mjphoto/cnc_machine_mj/CAD_Files/Bike Jump/JigSaw/M_Plus_Connect_to_Medium.png

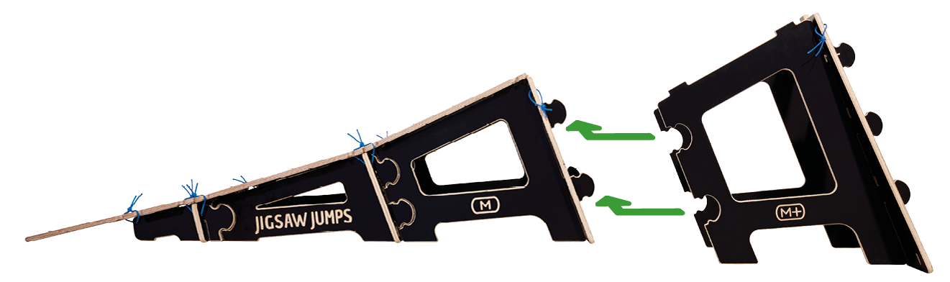
CAD_Files/Bike Jump/JigSaw/M_Plus_Connect_to_Medium.png
