mjphoto/cnc_machine_mj/CAD_Files/Bike Jump/JigSaw/M_Plus_Diagram.png

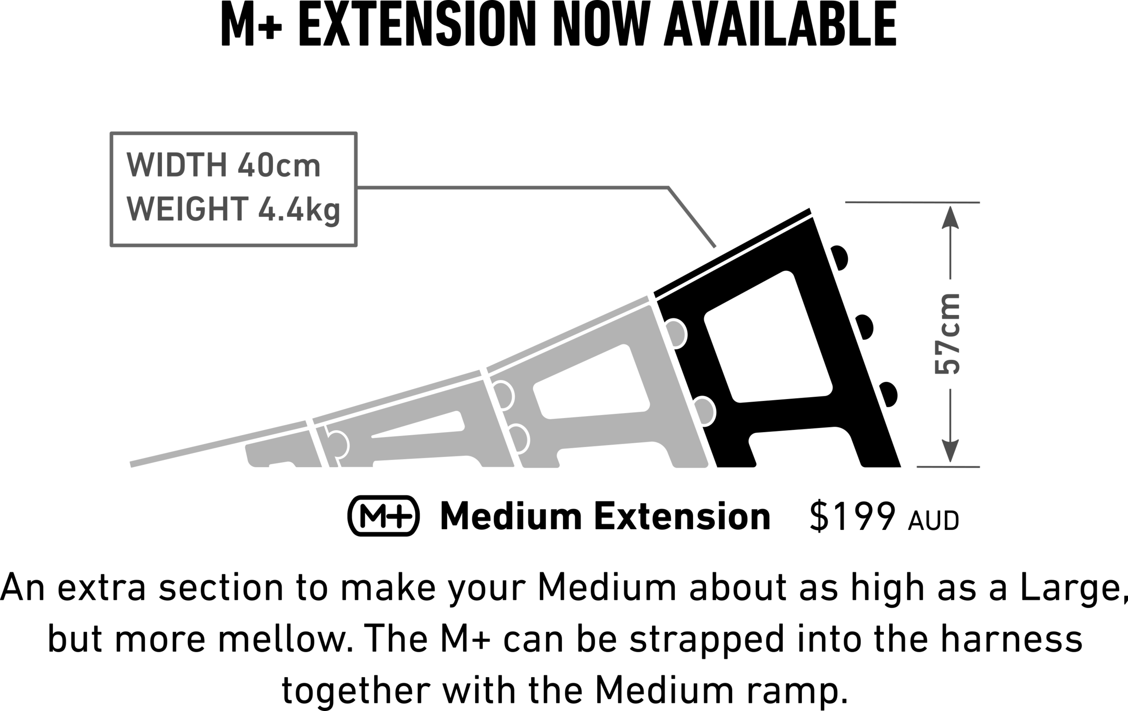
CAD_Files/Bike Jump/JigSaw/M_Plus_Diagram.png
