mjphoto/cnc_machine_mj/CAD_Files/Bike Jump/MTB Hopper/Coac and Extension.PNG

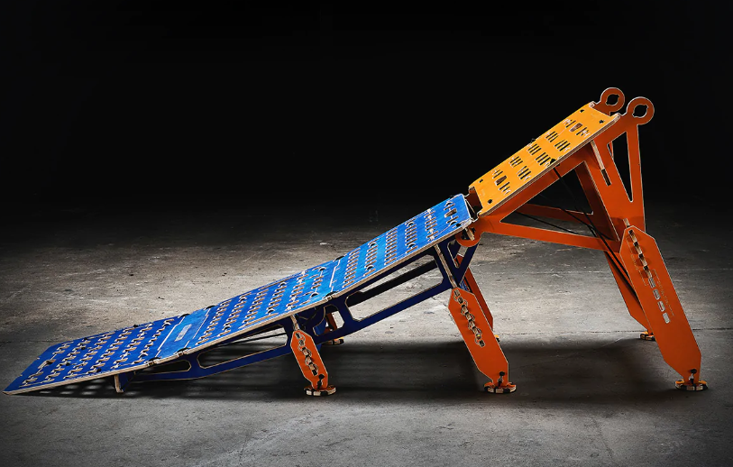
CAD_Files/Bike Jump/MTB Hopper/Coac and Extension.PNG
