mjphoto/cnc_machine_mj/CAD_Files/Bike Jump/MTB Hopper/Coach High.PNG

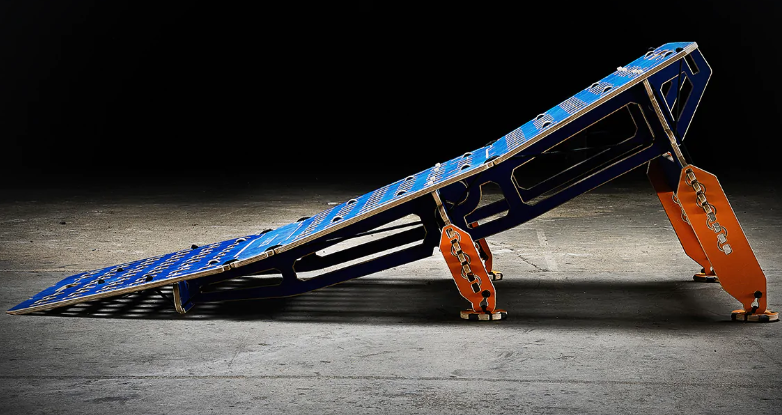
CAD_Files/Bike Jump/MTB Hopper/Coach High.PNG
