mjphoto/cnc_machine_mj/CAD_Files/Bike Jump/MTB Hopper/LITE.webp

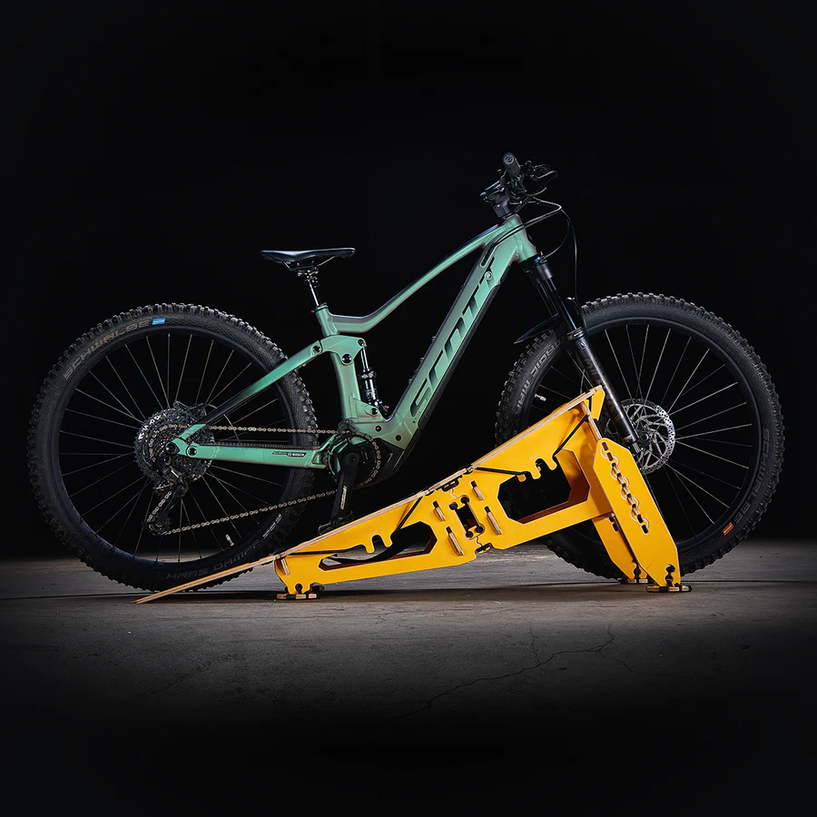
CAD_Files/Bike Jump/MTB Hopper/LITE.webp
