mjphoto/cnc_machine_mj/eyebrows/side_1655.dxf

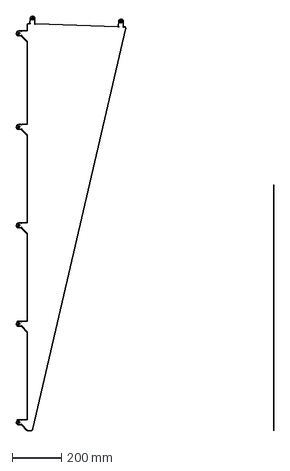
[picture p28: CAD file, 2020-05-06]
eyebrows/side_1655.dxf
1045.0 x 1684.5 mm
