mjphoto/cnc_machine_mj/CAD_CNC_Machine/CNC_Machine_CAD_Short/C-Beam End Plate.SLDPRT

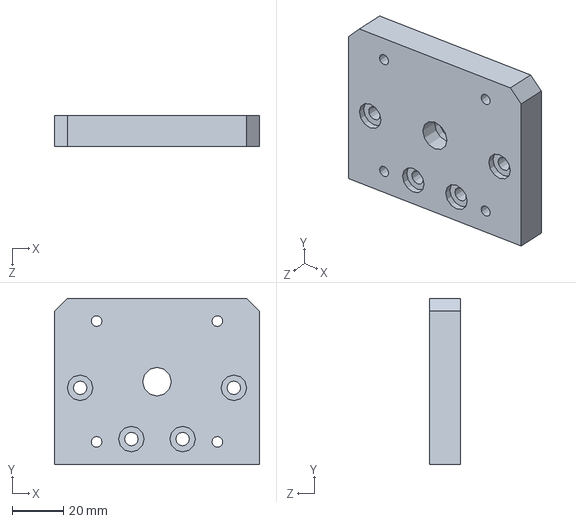
[picture p29: CAD file, 2023-01-13]
CAD_CNC_Machine/CNC_Machine_CAD_Short/C-Beam End Plate.SLDPRT
80.0 x 64.9 x 12.0 mm
