mjphoto/cnc_machine_mj/CAD_Files/Bike Jump/PBR-CON-001.SLDPRT

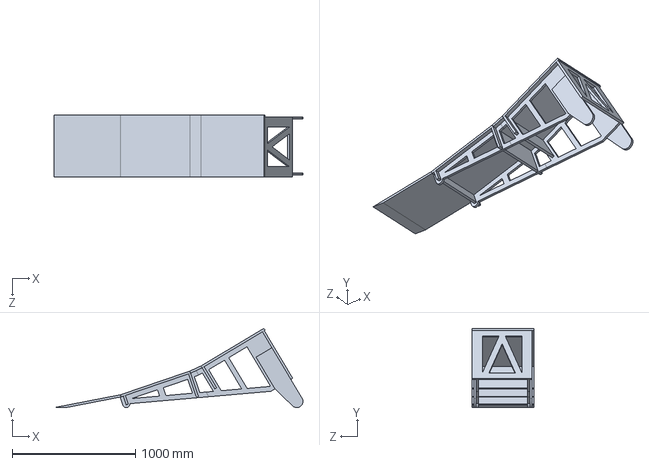
[picture p30: CAD file, 2022-08-21]
CAD_Files/Bike Jump/PBR-CON-001.SLDPRT
2021.9 x 643.9 x 500.0 mm
