mjphoto/cnc_machine_mj/CAD_Files/CNC Clamps/Clamp_130mm.STEP

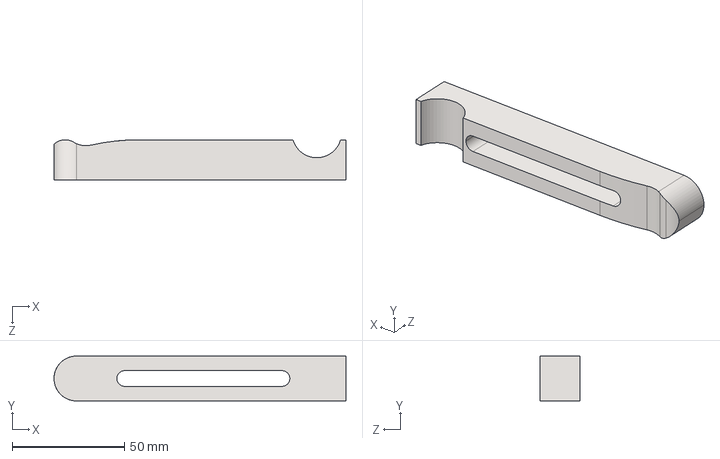
[picture p31: CAD file, 2022-08-21]
CAD_Files/CNC Clamps/Clamp_130mm.STEP
130.0 x 20.0 x 18.0 mm
