mjphoto/cnc_machine_mj/CAD_Files/Kitchen Cupboard/Wardrobe_Bench.STEP

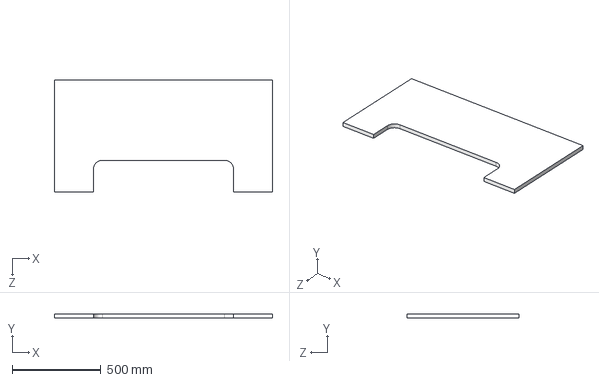
[picture p32: CAD file, 2022-09-03]
CAD_Files/Kitchen Cupboard/Wardrobe_Bench.STEP
1225.0 x 25.0 x 627.0 mm
