mjphoto/cnc_machine_mj/CAD_Files/Workbench/BenchWheelSpacer-Boss-Extrude4.STEP

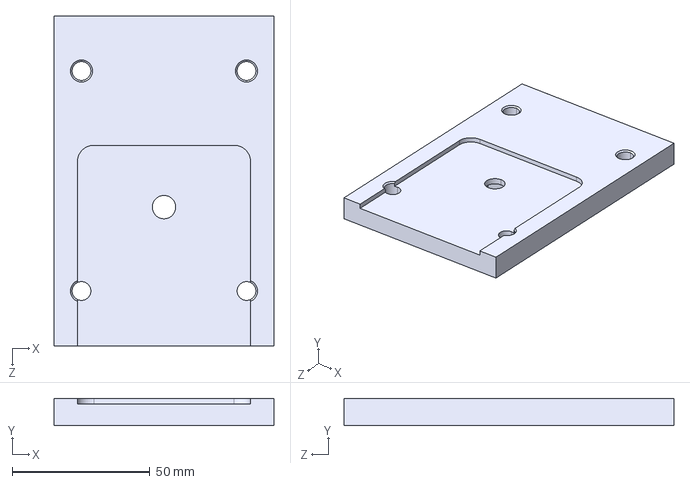
[picture p33: CAD file, 2022-08-21]
CAD_Files/Workbench/BenchWheelSpacer-Boss-Extrude4.STEP
80.0 x 10.0 x 120.0 mm
