mjphoto/cnc_machine_mj/eyebrows/side_2295.dxf

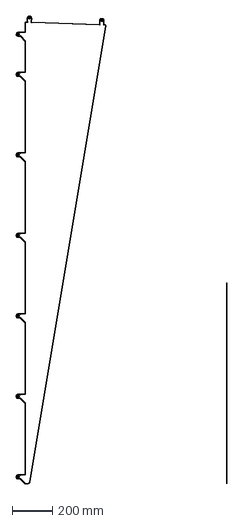
[picture p34: CAD file, 2020-05-06]
eyebrows/side_2295.dxf
1045.0 x 2324.4 mm
