mjphoto/cnc_machine_mj/CAD_Files/CNC Clamps/Clamp_110mm.STEP

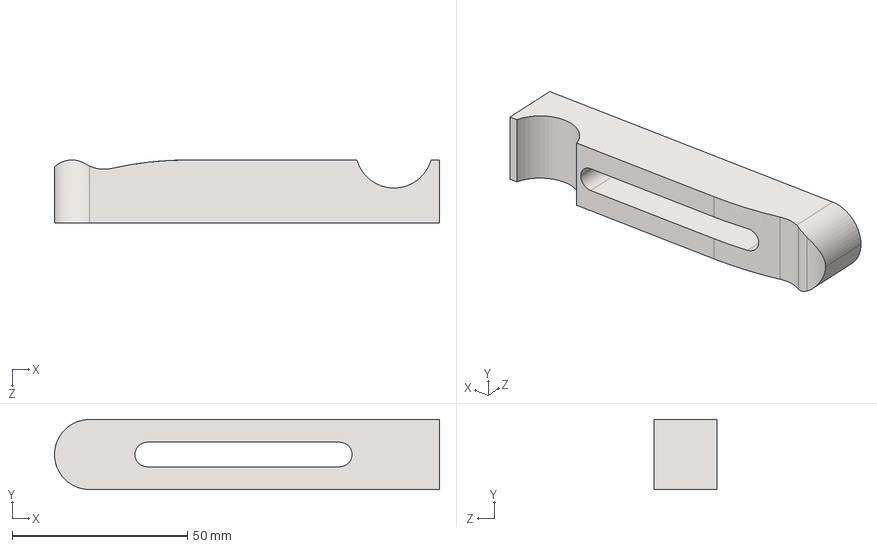
[picture p35: CAD file, 2022-08-21]
CAD_Files/CNC Clamps/Clamp_110mm.STEP
110.0 x 20.0 x 18.0 mm
