mjphoto/cnc_machine_mj/CAD_Files/Kitchen Cupboard/NEstyboi.STEP

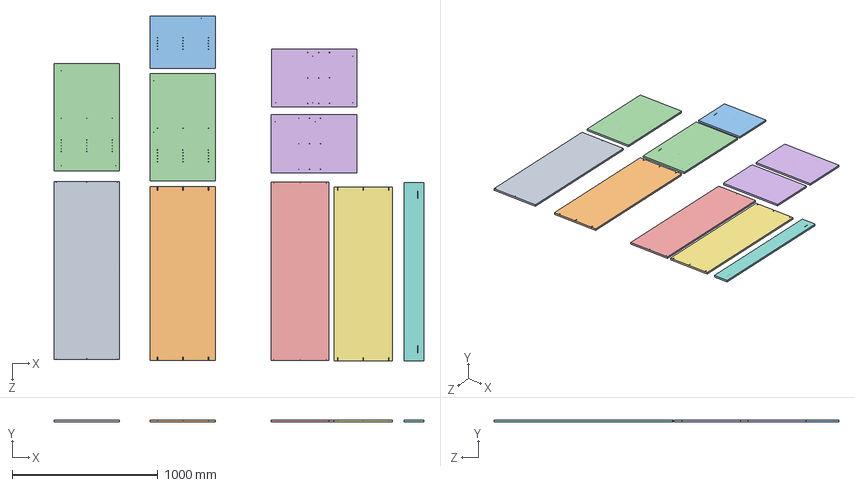
[picture p36: CAD file, 2022-09-02]
CAD_Files/Kitchen Cupboard/NEstyboi.STEP
2541.8 x 16.0 x 2369.9 mm
Wardrobe_02
Wardrobe_03
Wardrobe_04
Wardrobe_05
Wardrobe_06
Wardrobe_07
Wardrobe_08
Wardrobe_09
Wardrobe_10
Wardrobe_11
