mjphoto/cnc_machine_mj/eyebrows/side_2235.dxf

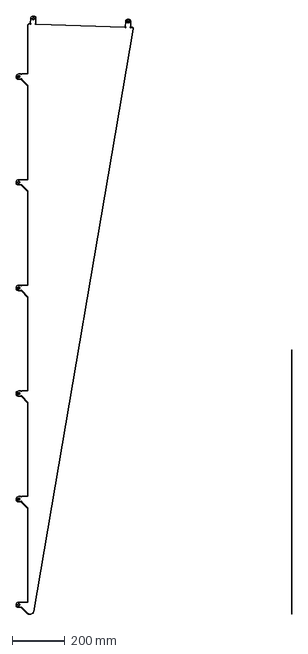
[picture p37: CAD file, 2020-05-06]
eyebrows/side_2235.dxf
1045.0 x 2264.5 mm
