mjphoto/cnc_machine_mj/CAD_Files/Baby Play Gym/PlayGym_Side_A.STEP

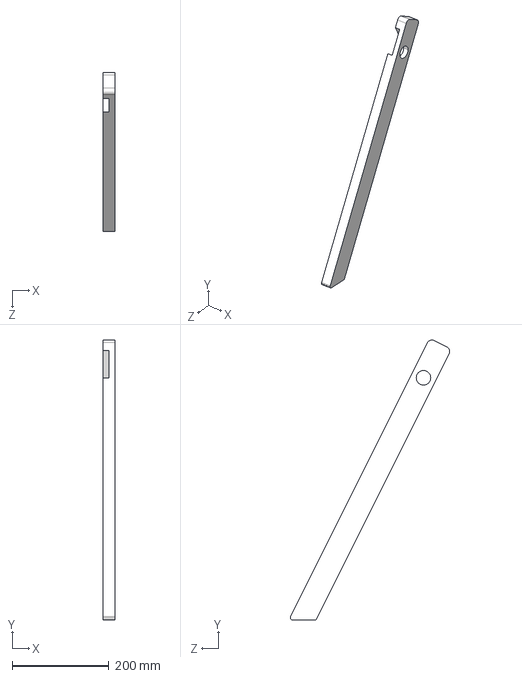
[picture p38: CAD file, 2022-09-02]
CAD_Files/Baby Play Gym/PlayGym_Side_A.STEP
25.0 x 578.0 x 328.9 mm
