mjphoto/cnc_machine_mj/eyebrows/side_1855.dxf

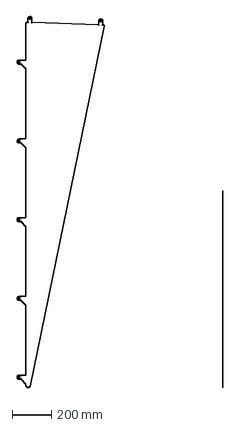
[picture p39: CAD file, 2020-05-06]
eyebrows/side_1855.dxf
1045.0 x 1884.5 mm
