mjphoto/cnc_machine_mj/CAD_CNC_Machine/CNC_Machine_CAD_Short/CNC_SHORT_MGN12H1R100ZFC.SLDPRT

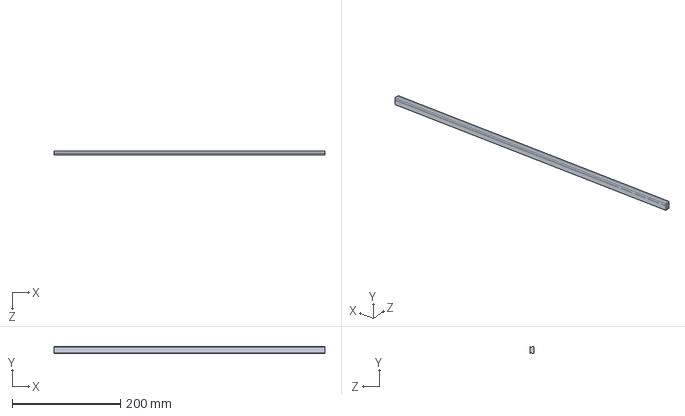
[picture p40: CAD file, 2023-01-13]
CAD_CNC_Machine/CNC_Machine_CAD_Short/CNC_SHORT_MGN12H1R100ZFC.SLDPRT
500.0 x 12.0 x 8.00 mm
