mjphoto/cnc_machine_mj/eyebrows/Verandah_plates.dxf

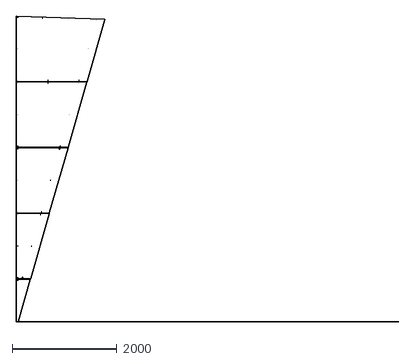
[picture p41: CAD file, 2020-05-05]
eyebrows/Verandah_plates.dxf
7301.5 x 5836.0
