mjphoto/cnc_machine_mj/CAD_CNC_Machine/CNC_Machine_CAD_Short/V-Slot C-Beam.SLDPRT

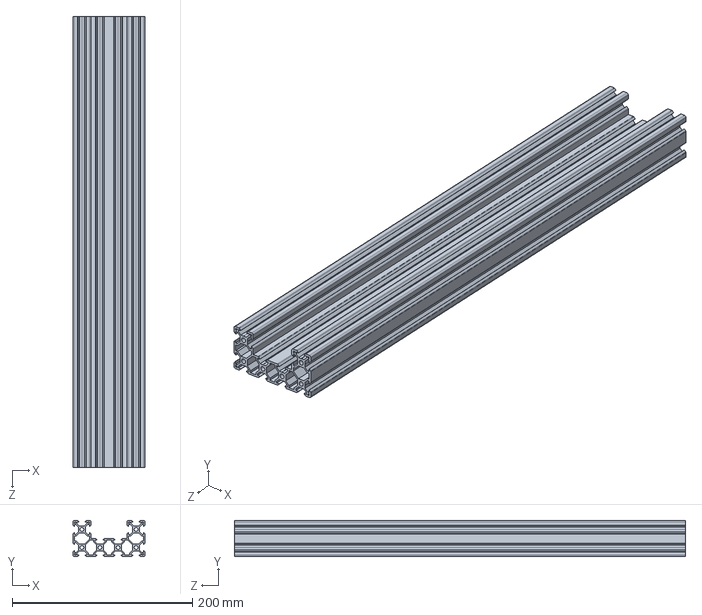
[picture p42: CAD file, 2023-01-13]
CAD_CNC_Machine/CNC_Machine_CAD_Short/V-Slot C-Beam.SLDPRT
80.0 x 40.0 x 500.0 mm
