mjphoto/cnc_machine_mj/CAD_CNC_Machine/CNC_Machine_CAD_Short/CNC_SHORT_X Axis Tall Front Plate_6mm - Build 80_11.15.14.SLDPRT

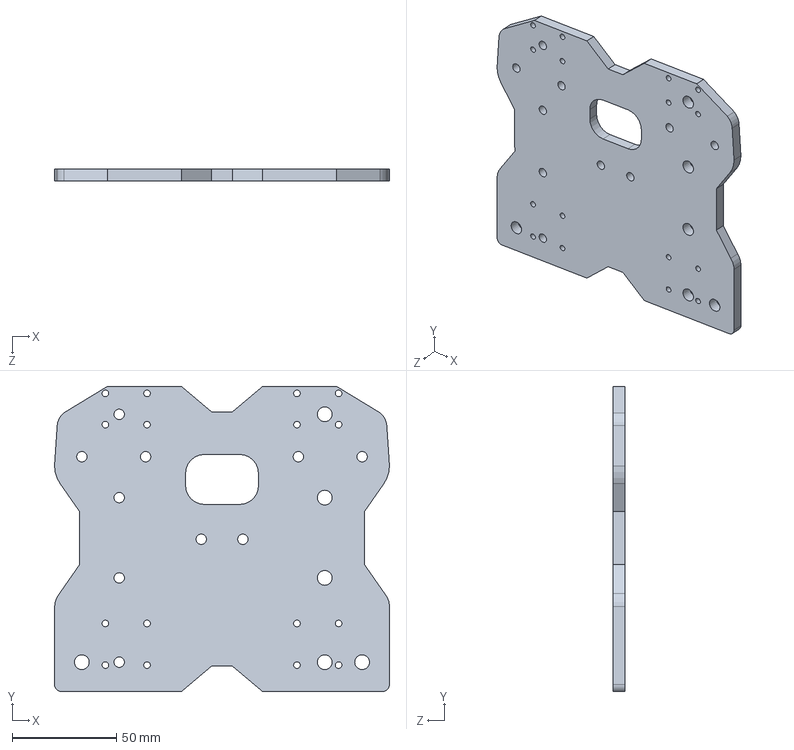
[picture p43: CAD file, 2023-01-13]
CAD_CNC_Machine/CNC_Machine_CAD_Short/CNC_SHORT_X Axis Tall Front Plate_6mm - Build 80_11.15.14.SLDPRT
160.9 x 146.5 x 6.00 mm
