mjphoto/cnc_machine_mj/CAD_CNC_Machine/CNC_Machine_CAD_Short/CNC_SHORT_V-Slot 20x80x1500 Linear Rail.SLDPRT

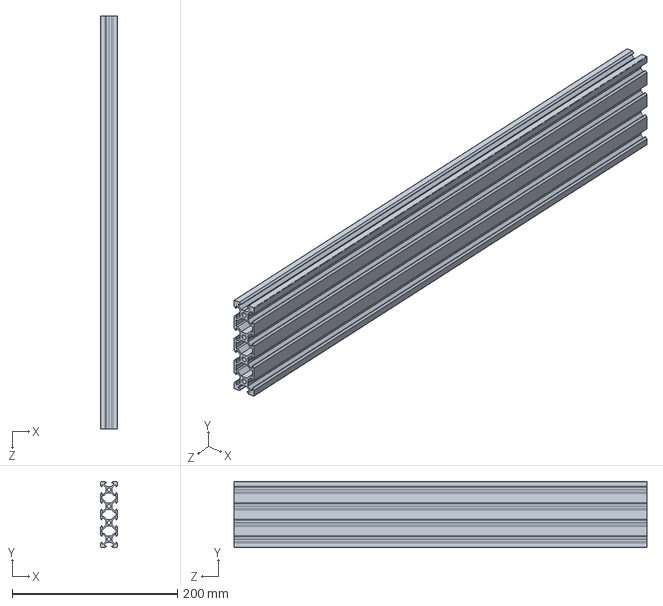
[picture p44: CAD file, 2022-12-09]
CAD_CNC_Machine/CNC_Machine_CAD_Short/CNC_SHORT_V-Slot 20x80x1500 Linear Rail.SLDPRT
20.0 x 80.0 x 500.0 mm
