mjphoto/cnc_machine_mj/CAD_CNC_Machine/CNC_Machine_CAD_Short/CNC_SHORT_Frame2.SLDPRT

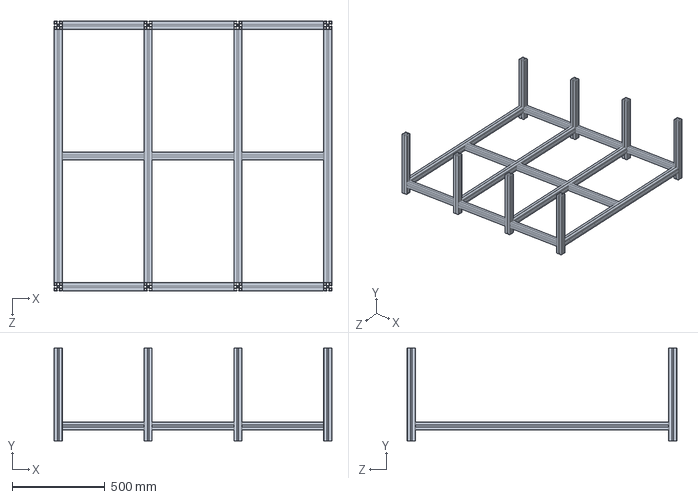
[picture p45: CAD file, 2022-12-09]
CAD_CNC_Machine/CNC_Machine_CAD_Short/CNC_SHORT_Frame2.SLDPRT
1500.0 x 500.0 x 1455.0 mm
