mjphoto/cnc_machine_mj/CAD_CNC_Machine/CNC_Machine_CAD_Short/CNC_SHORT_Table minitec.SLDPRT

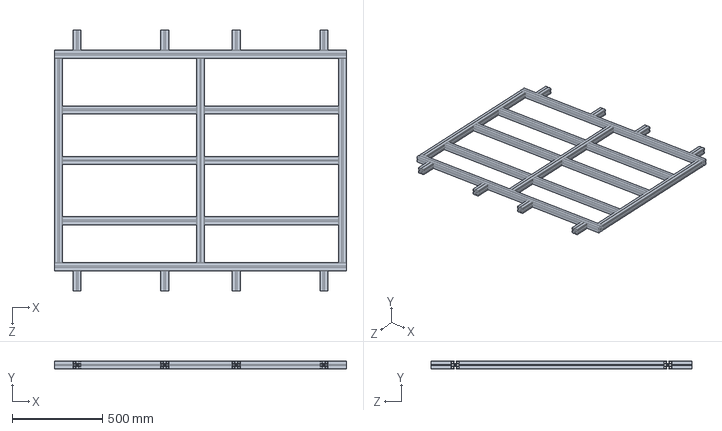
[picture p46: CAD file, 2022-12-09]
CAD_CNC_Machine/CNC_Machine_CAD_Short/CNC_SHORT_Table minitec.SLDPRT
1615.0 x 45.0 x 1445.0 mm
