mjphoto/cnc_machine_mj/CAD_CNC_Machine/CNC_Machine_CAD_Short/CNC_SHORT_V-Slot 20x40x1500 Linear Rail.SLDPRT

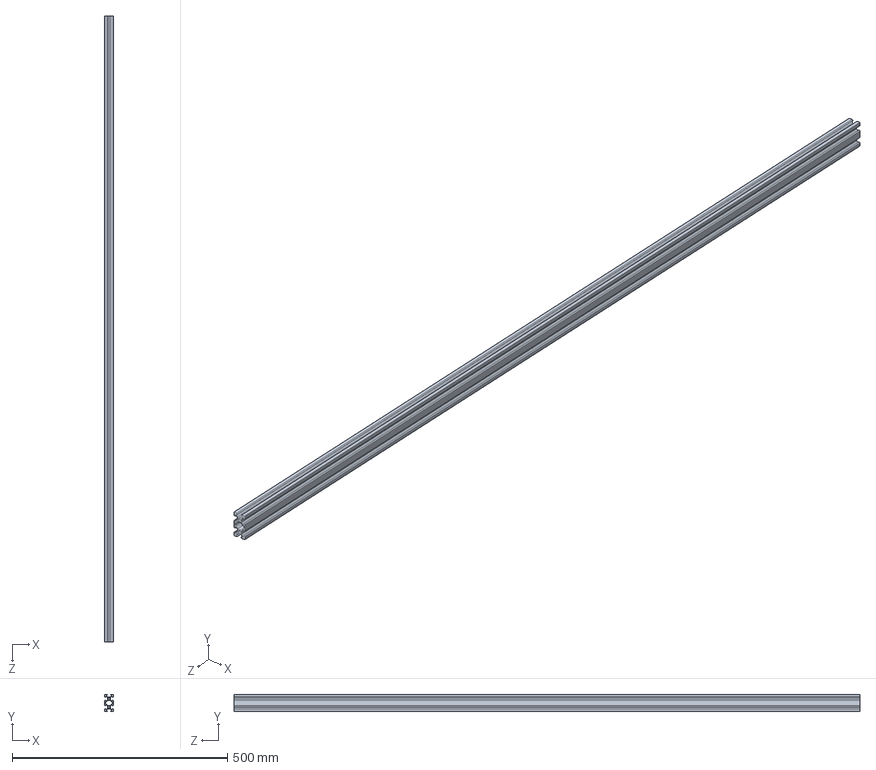
[picture p47: CAD file, 2022-12-09]
CAD_CNC_Machine/CNC_Machine_CAD_Short/CNC_SHORT_V-Slot 20x40x1500 Linear Rail.SLDPRT
20.0 x 40.0 x 1455.0 mm
