mjphoto/cnc_machine_mj/CAD_CNC_Machine/CNC_Machine_CAD_Short/CNC_SHORT_Eccentric Spacer 6mm.SLDPRT

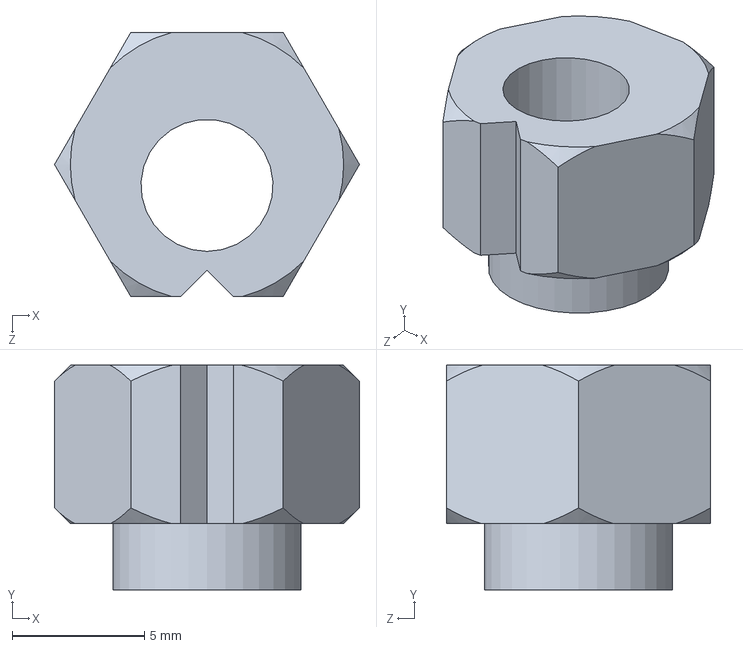
[picture p48: CAD file, 2022-11-07]
CAD_CNC_Machine/CNC_Machine_CAD_Short/CNC_SHORT_Eccentric Spacer 6mm.SLDPRT
11.5 x 8.50 x 10.0 mm
