mjphoto/cnc_machine_mj/CAD_CNC_Machine/CNC_Machine_CAD_Short/CNC_SHORT_GT3 Timing Pulley 20 Tooth.SLDPRT

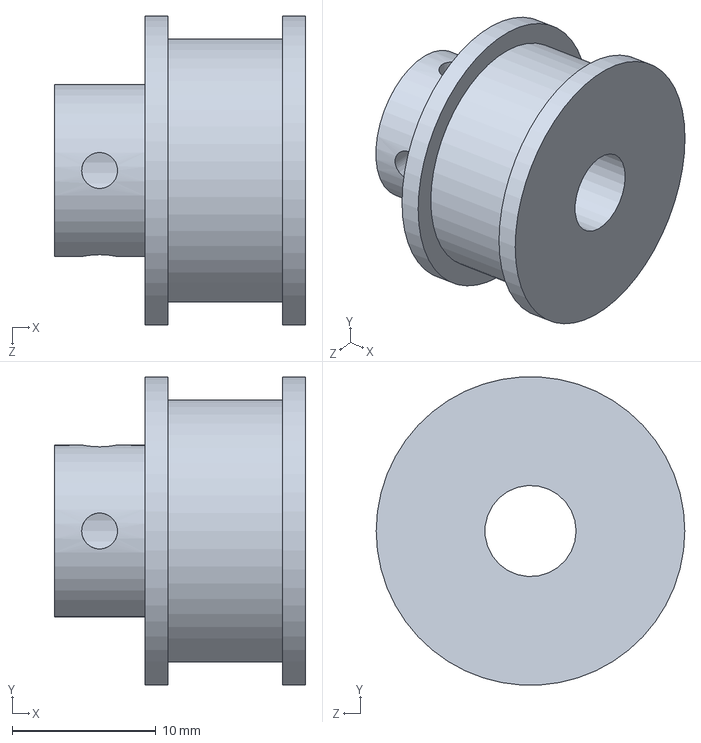
[picture p49: CAD file, 2022-11-07]
CAD_CNC_Machine/CNC_Machine_CAD_Short/CNC_SHORT_GT3 Timing Pulley 20 Tooth.SLDPRT
17.5 x 21.5 x 21.5 mm
