mjphoto/cnc_machine_mj/CAD_CNC_Machine/CNC_Machine_CAD_Short/CNC_SHORT_Aluminum Spacer 9mm.SLDPRT

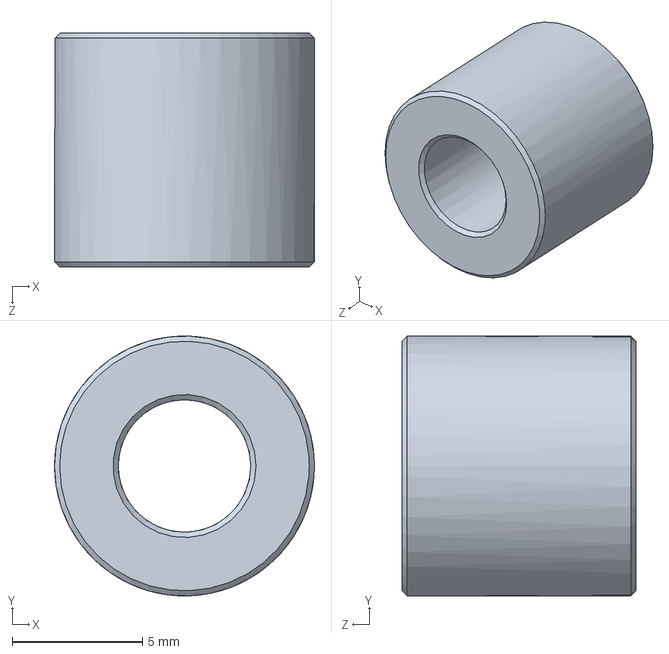
[picture p50: CAD file, 2022-11-07]
CAD_CNC_Machine/CNC_Machine_CAD_Short/CNC_SHORT_Aluminum Spacer 9mm.SLDPRT
10.0 x 9.99 x 9.00 mm
