mjphoto/cnc_machine_mj/CAD_CNC_Machine/CNC_Machine_CAD_Short/CNC_SHORT_Spindle.SLDPRT

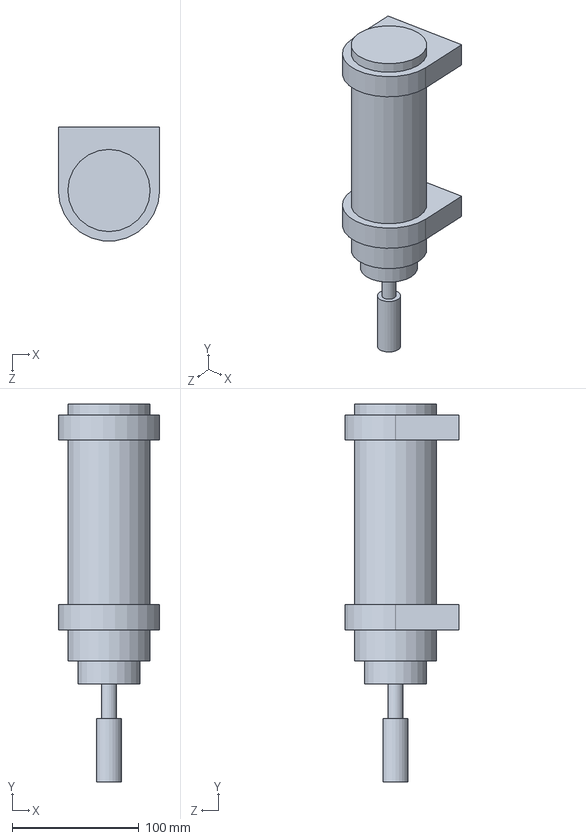
[picture p51: CAD file, 2022-11-07]
CAD_CNC_Machine/CNC_Machine_CAD_Short/CNC_SHORT_Spindle.SLDPRT
80.0 x 298.5 x 89.7 mm
