mjphoto/cnc_machine_mj/CAD_CNC_Machine/CNC_Machine_CAD_Short/CNC_SHORT_Spoil.SLDPRT

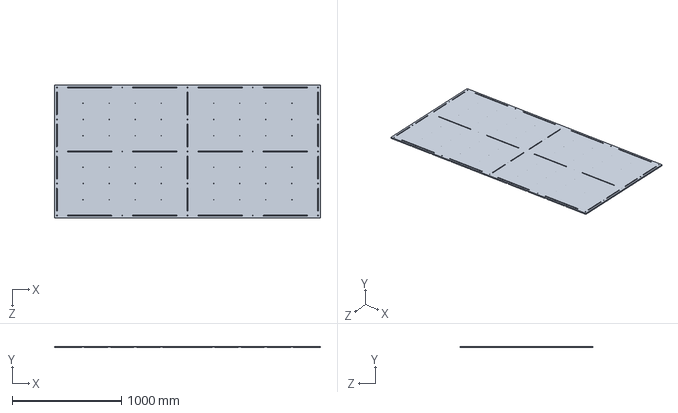
[picture p52: CAD file, 2022-11-07]
CAD_CNC_Machine/CNC_Machine_CAD_Short/CNC_SHORT_Spoil.SLDPRT
2440.0 x 12.0 x 1220.0 mm
