mjphoto/cnc_machine_mj/CAD_CNC_Machine/CNC_Machine_CAD_Short/CNC_SHORT_Precision Shim 10 x 5 x 1.SLDPRT

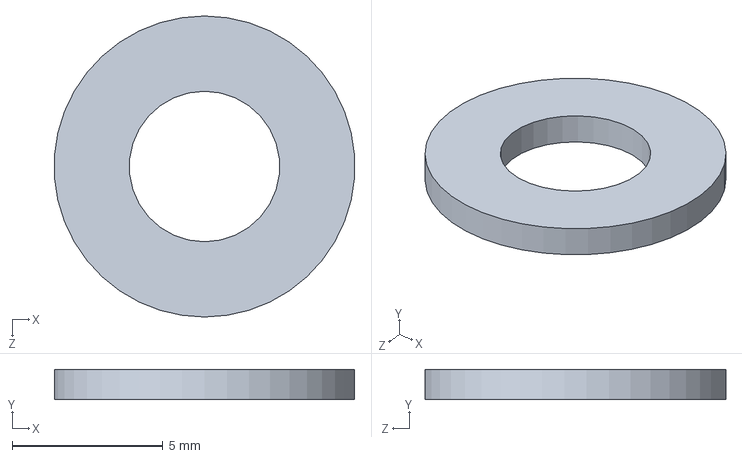
[picture p53: CAD file, 2022-11-07]
CAD_CNC_Machine/CNC_Machine_CAD_Short/CNC_SHORT_Precision Shim 10 x 5 x 1.SLDPRT
9.97 x 1.00 x 10.0 mm
