mjphoto/cnc_machine_mj/CAD_CNC_Machine/CNC_Machine_CAD_Short/CNC_SHORT_Y Gantry Plate_6mm - Build 80_11.15.14.SLDPRT

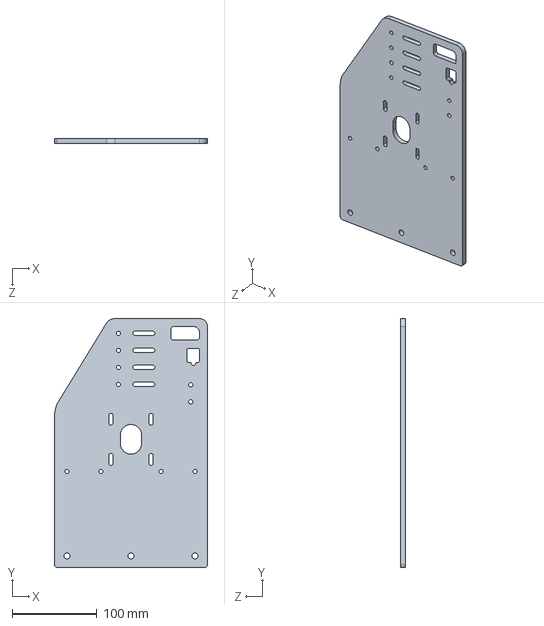
[picture p54: CAD file, 2022-11-07]
CAD_CNC_Machine/CNC_Machine_CAD_Short/CNC_SHORT_Y Gantry Plate_6mm - Build 80_11.15.14.SLDPRT
180.0 x 293.0 x 6.00 mm
