mjphoto/cnc_machine_mj/CAD_CNC_Machine/CNC_Machine_CAD_Short/CNC_SHORT_Spindle Holder.SLDPRT

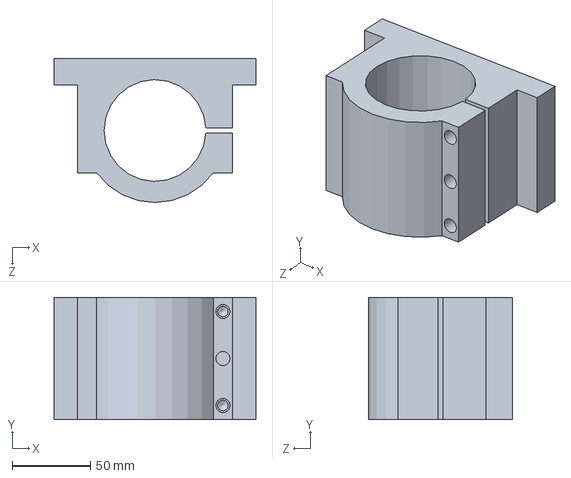
[picture p55: CAD file, 2022-11-07]
CAD_CNC_Machine/CNC_Machine_CAD_Short/CNC_SHORT_Spindle Holder.SLDPRT
129.0 x 78.0 x 92.0 mm
