mjphoto/cnc_machine_mj/CAD_CNC_Machine/CNC_Machine_CAD_Short/CNC_SHORT_Tensioning Bracket.SLDPRT

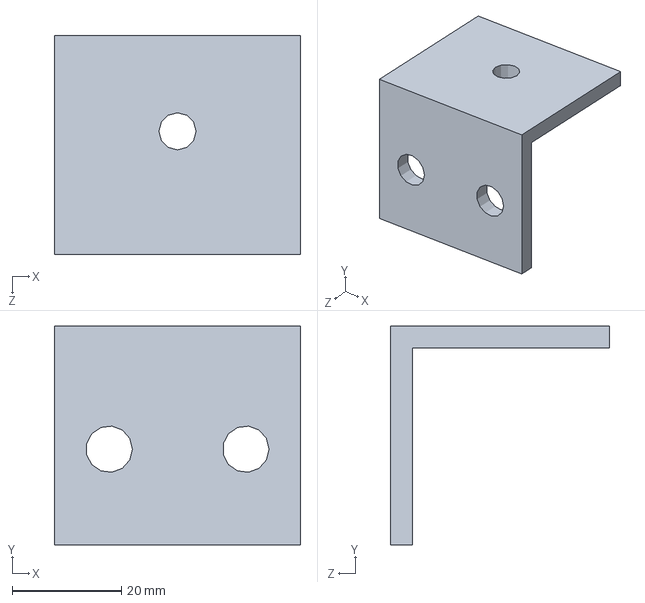
[picture p56: CAD file, 2022-11-07]
CAD_CNC_Machine/CNC_Machine_CAD_Short/CNC_SHORT_Tensioning Bracket.SLDPRT
45.0 x 40.0 x 40.0 mm
