mjphoto/cnc_machine_mj/CAD_CNC_Machine/CNC_Machine_CAD_Short/CNC_SHORT_2020.SLDPRT

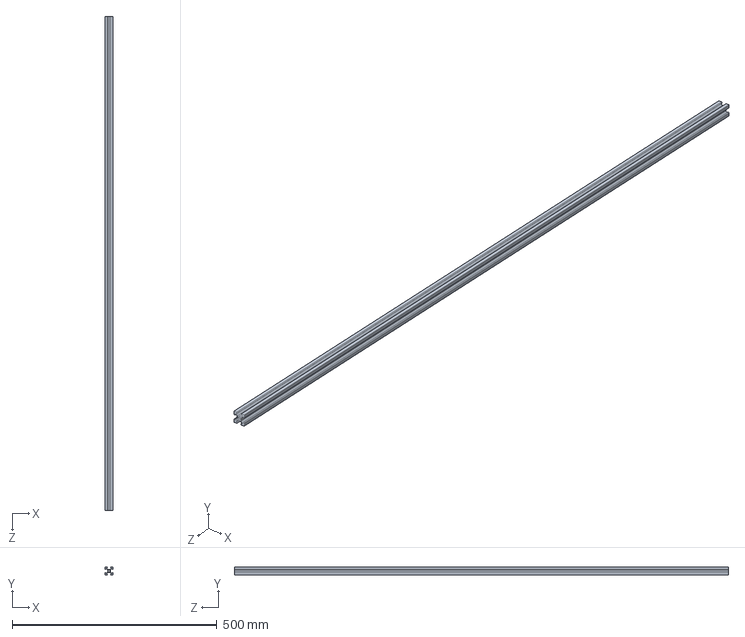
[picture p57: CAD file, 2022-11-07]
CAD_CNC_Machine/CNC_Machine_CAD_Short/CNC_SHORT_2020.SLDPRT
20.0 x 20.0 x 1205.0 mm
