mjphoto/cnc_machine_mj/CAD_CNC_Machine/CNC_Machine_CAD_Short/CNC_SHORT_Nema 23 Stepper Motor.SLDPRT

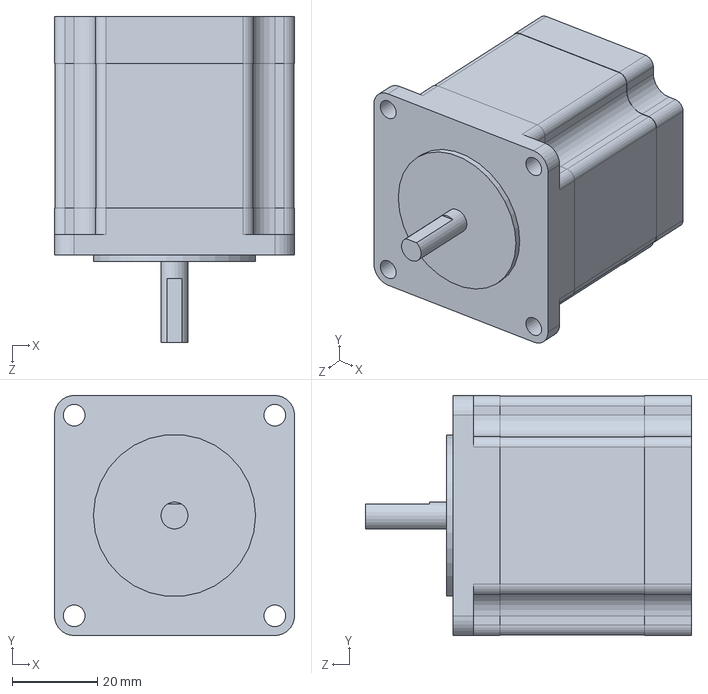
[picture p58: CAD file, 2022-11-07]
CAD_CNC_Machine/CNC_Machine_CAD_Short/CNC_SHORT_Nema 23 Stepper Motor.SLDPRT
56.4 x 56.4 x 76.6 mm
