mjphoto/cnc_machine_mj/CAD_CNC_Machine/CNC_Machine_CAD_Short/CNC_SHORT_Aluminium bed threaded bar.SLDPRT

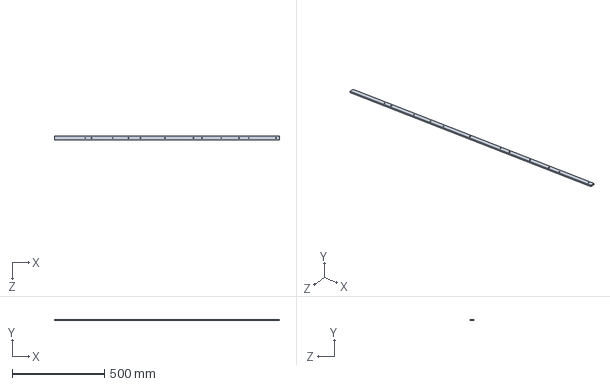
[picture p59: CAD file, 2022-11-07]
CAD_CNC_Machine/CNC_Machine_CAD_Short/CNC_SHORT_Aluminium bed threaded bar.SLDPRT
1220.0 x 6.00 x 20.0 mm
