mjphoto/cnc_machine_mj/CAD_CNC_Machine/CNC_Machine_CAD_Short/CNC_SHORT_L Bracket Single.SLDPRT

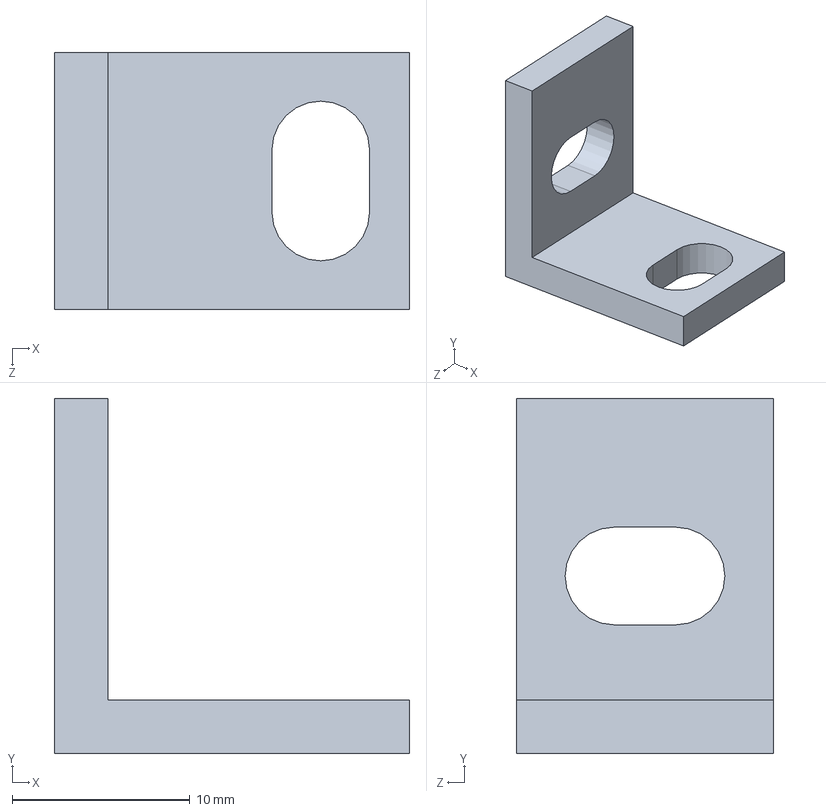
[picture p60: CAD file, 2022-11-07]
CAD_CNC_Machine/CNC_Machine_CAD_Short/CNC_SHORT_L Bracket Single.SLDPRT
20.0 x 20.0 x 14.5 mm
