mjphoto/cnc_machine_mj/CAD_CNC_Machine/CNC_Machine_CAD_Short/CNC_SHORT_MGN15H1R100ZFC.SLDPRT

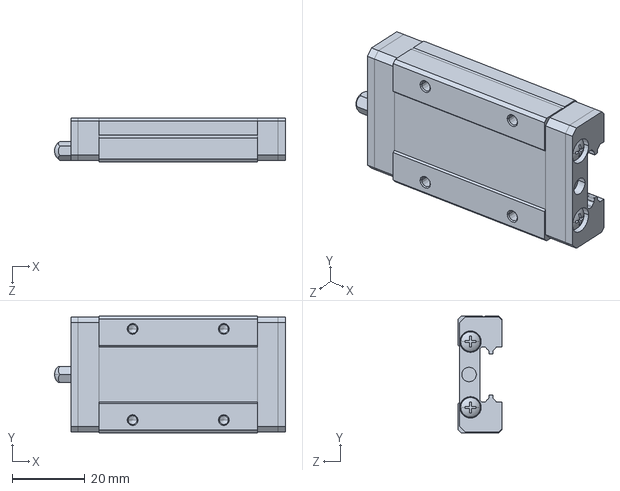
[picture p61: CAD file, 2022-11-07]
CAD_CNC_Machine/CNC_Machine_CAD_Short/CNC_SHORT_MGN15H1R100ZFC.SLDPRT
63.3 x 32.0 x 12.0 mm
