mjphoto/cnc_machine_mj/CAD_CNC_Machine/CNC_Machine_CAD_Short/CNC_SHORT_Aluminum Spacer 40mm.SLDPRT

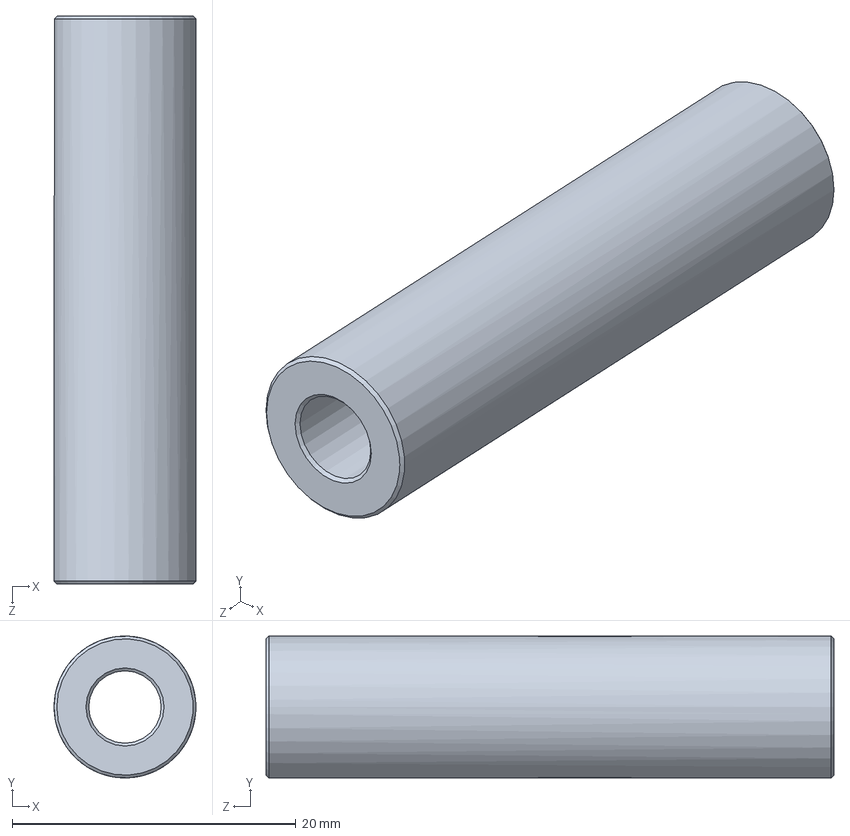
[picture p62: CAD file, 2022-11-07]
CAD_CNC_Machine/CNC_Machine_CAD_Short/CNC_SHORT_Aluminum Spacer 40mm.SLDPRT
10.0 x 9.99 x 40.0 mm
