mjphoto/cnc_machine_mj/CAD_CNC_Machine/CNC_Machine_CAD_Short/CNC_SHORT_BedBoardV2.SLDPRT

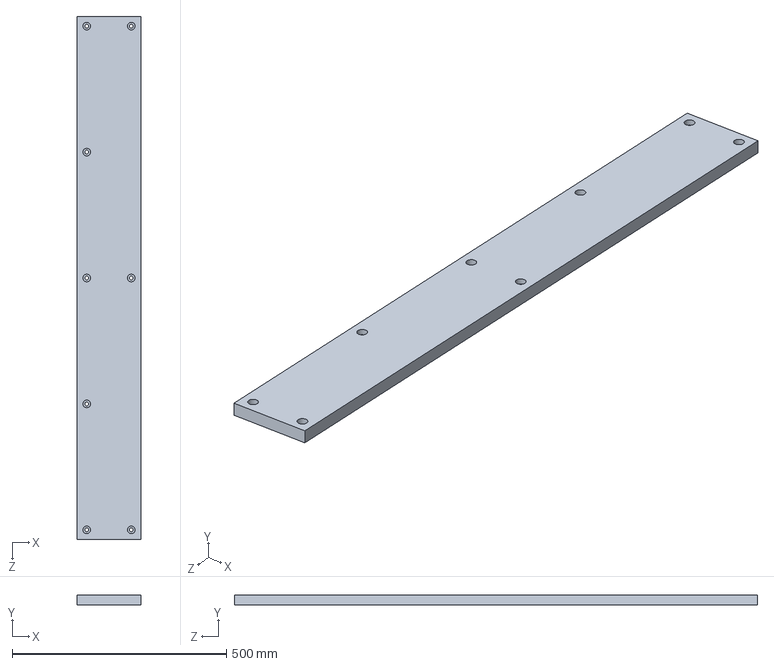
[picture p63: CAD file, 2022-11-07]
CAD_CNC_Machine/CNC_Machine_CAD_Short/CNC_SHORT_BedBoardV2.SLDPRT
148.9 x 23.0 x 1220.0 mm
