mjphoto/cnc_machine_mj/CAD_CNC_Machine/CNC_Machine_CAD_Short/CNC_SHORT_CNC-01-1015.SLDPRT

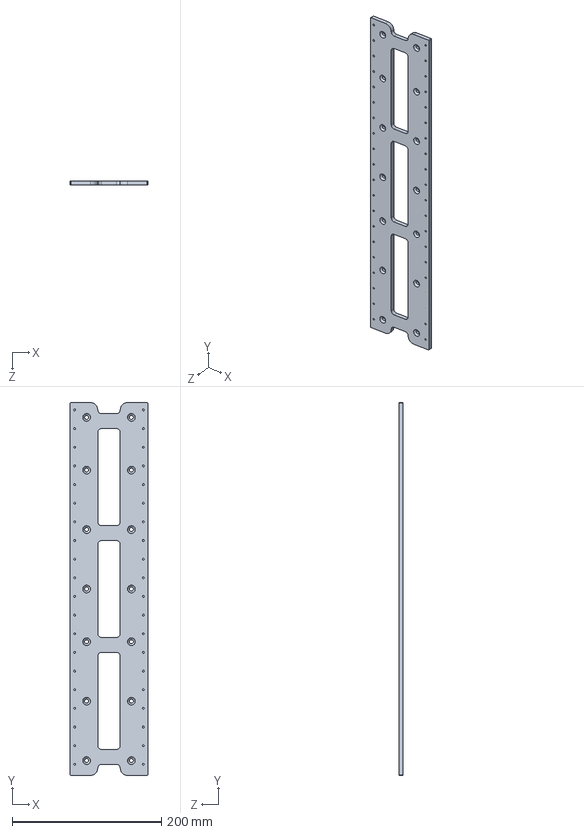
[picture p64: CAD file, 2022-11-07]
CAD_CNC_Machine/CNC_Machine_CAD_Short/CNC_SHORT_CNC-01-1015.SLDPRT
104.0 x 500.0 x 6.00 mm
