mjphoto/cnc_machine_mj/CAD_CNC_Machine/CNC_Machine_CAD_Short/CNC_SHORT_Lock Collar 8mm.SLDPRT

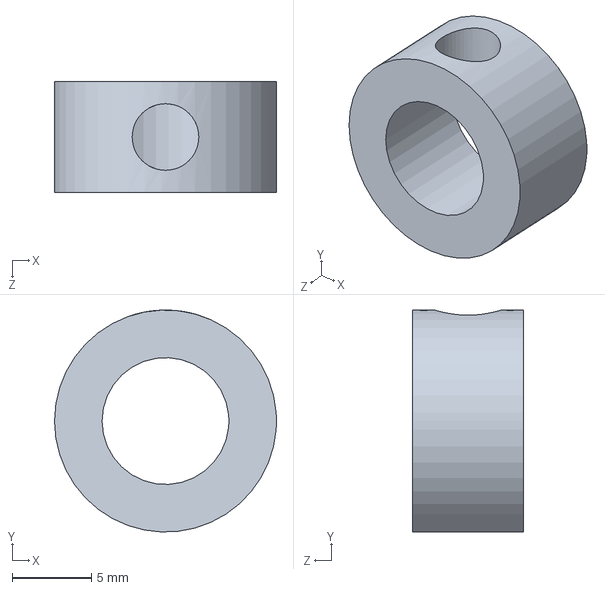
[picture p65: CAD file, 2022-11-07]
CAD_CNC_Machine/CNC_Machine_CAD_Short/CNC_SHORT_Lock Collar 8mm.SLDPRT
14.0 x 14.0 x 7.00 mm
