mjphoto/cnc_machine_mj/CAD_CNC_Machine/CNC_Machine_CAD_Short/CNC_SHORT_MGN12C1R100ZFC.SLDPRT

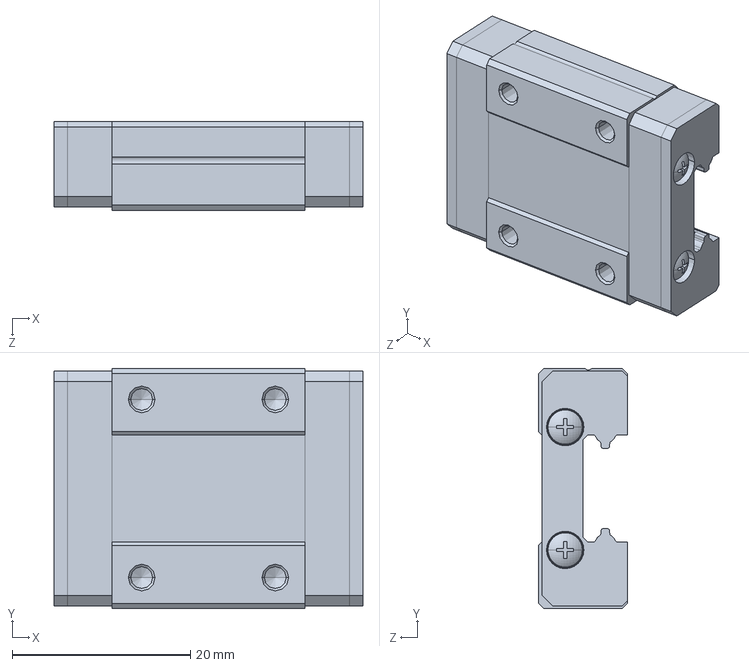
[picture p66: CAD file, 2022-11-07]
CAD_CNC_Machine/CNC_Machine_CAD_Short/CNC_SHORT_MGN12C1R100ZFC.SLDPRT
34.7 x 27.0 x 10.0 mm
