mjphoto/cnc_machine_mj/CAD_CNC_Machine/CNC_Machine_CAD_Short/CNC_SHORT_Micro Limit Switch.SLDPRT

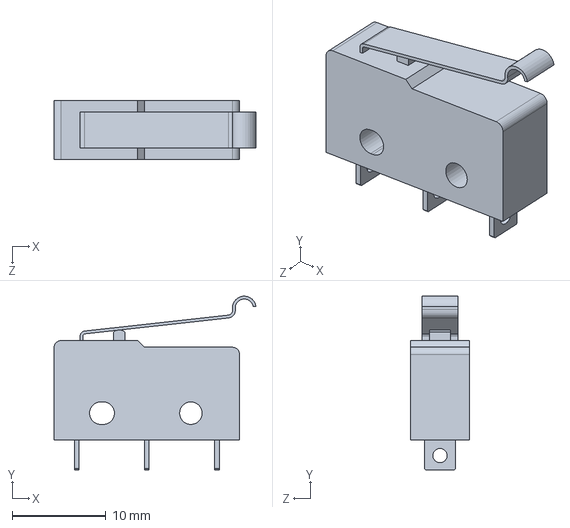
[picture p67: CAD file, 2022-11-07]
CAD_CNC_Machine/CNC_Machine_CAD_Short/CNC_SHORT_Micro Limit Switch.SLDPRT
21.6 x 18.6 x 6.35 mm
