mjphoto/cnc_machine_mj/CAD_CNC_Machine/CNC_Machine_CAD_Short/CNC_SHORT_COLLET ER11 d6-.SLDPRT

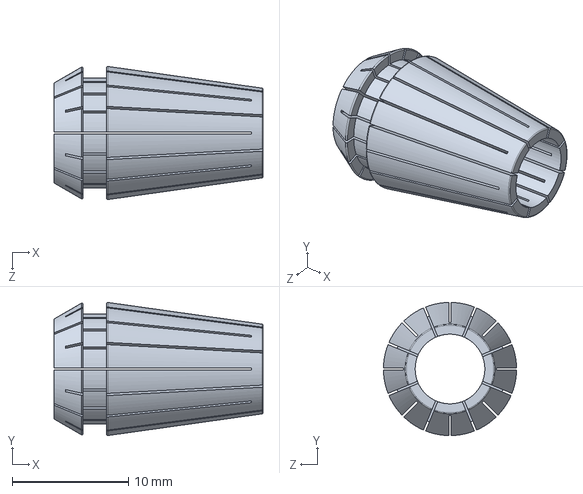
[picture p68: CAD file, 2022-11-07]
CAD_CNC_Machine/CNC_Machine_CAD_Short/CNC_SHORT_COLLET ER11 d6-.SLDPRT
18.0 x 11.5 x 11.5 mm
