mjphoto/cnc_machine_mj/CAD_CNC_Machine/CNC_Machine_CAD_Short/CNC_SHORT_Angle Bracket - 2080-4545.SLDPRT

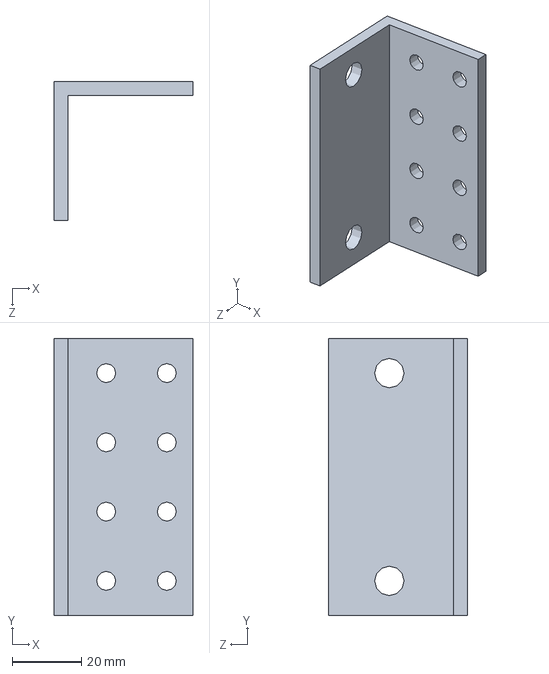
[picture p69: CAD file, 2022-11-07]
CAD_CNC_Machine/CNC_Machine_CAD_Short/CNC_SHORT_Angle Bracket - 2080-4545.SLDPRT
40.0 x 80.0 x 40.0 mm
