mjphoto/cnc_machine_mj/CAD_CNC_Machine/CNC_Machine_CAD_Short/CNC_SHORT_TeeBrace.SLDPRT

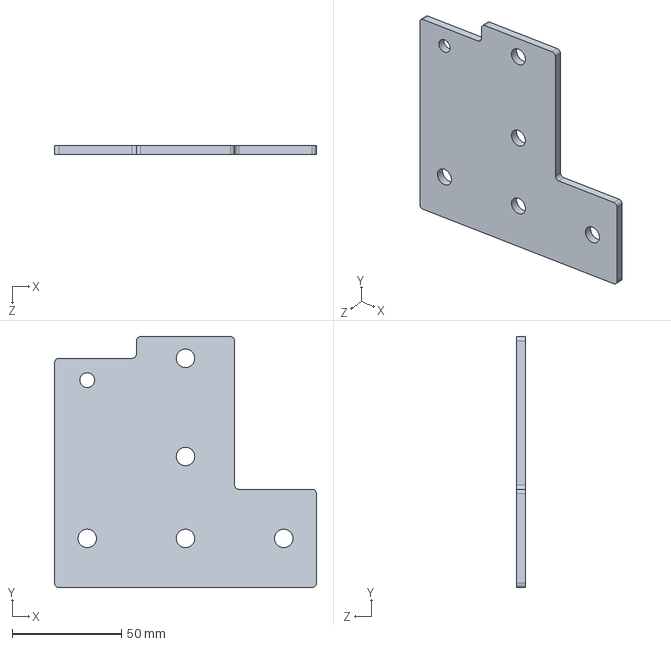
[picture p70: CAD file, 2022-11-07]
CAD_CNC_Machine/CNC_Machine_CAD_Short/CNC_SHORT_TeeBrace.SLDPRT
120.0 x 115.0 x 4.00 mm
