mjphoto/cnc_machine_mj/CAD_CNC_Machine/CNC_Machine_CAD_Short/CNC_SHORT_spacer block large.SLDPRT

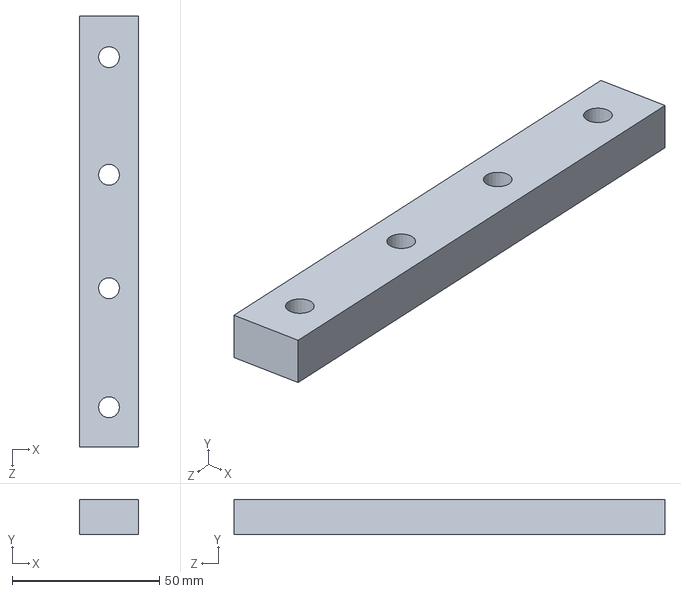
[picture p71: CAD file, 2022-11-07]
CAD_CNC_Machine/CNC_Machine_CAD_Short/CNC_SHORT_spacer block large.SLDPRT
20.0 x 12.0 x 146.5 mm
