mjphoto/cnc_machine_mj/CAD_CNC_Machine/CNC_Machine_CAD_Short/CNC_SHORT_Фреза.SLDPRT

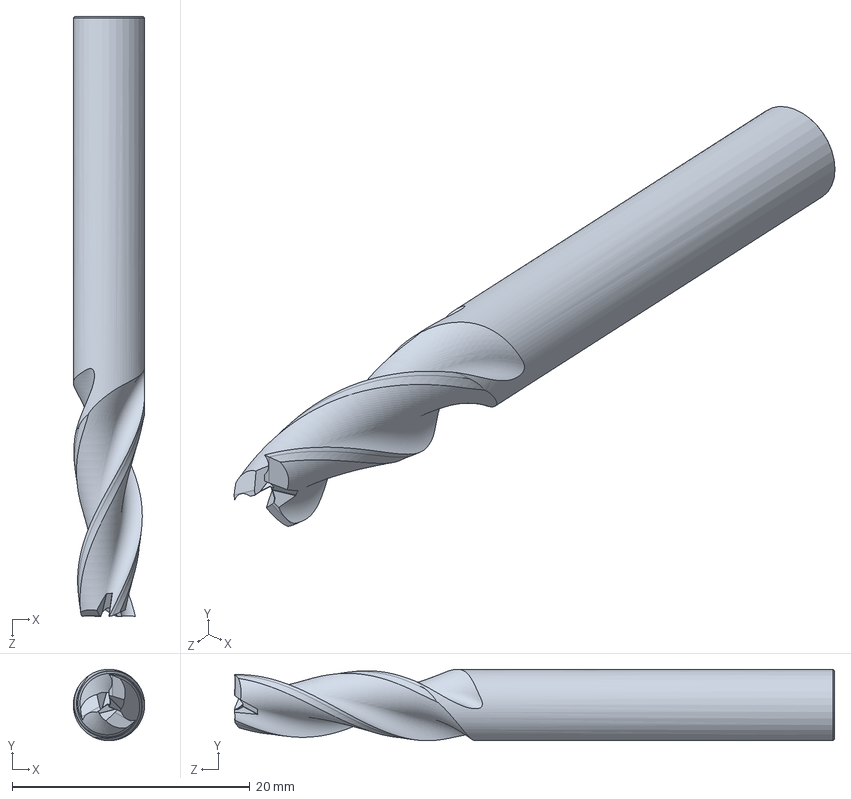
[picture p72: CAD file, 2022-11-07]
CAD_CNC_Machine/CNC_Machine_CAD_Short/CNC_SHORT_Фреза.SLDPRT
6.00 x 6.00 x 50.4 mm
