mjphoto/cnc_machine_mj/CAD_CNC_Machine/CNC_Machine_CAD_Short/CNC_SHORT_Flexible Coupling 0.25in x 8mm.SLDPRT

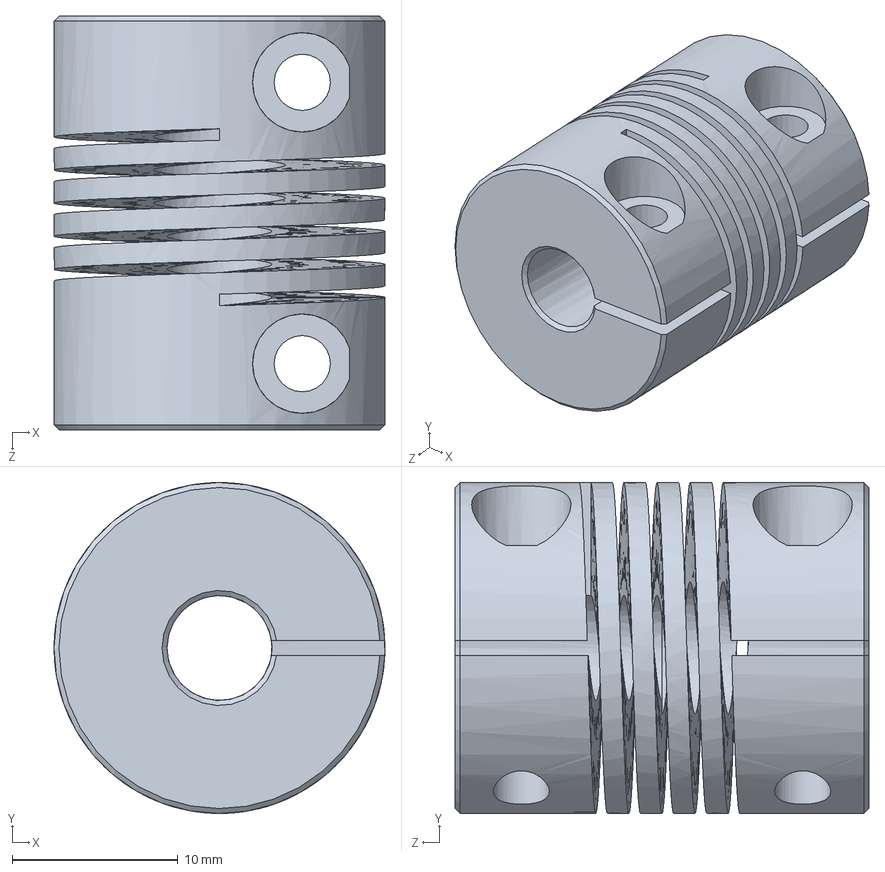
[picture p73: CAD file, 2022-11-07]
CAD_CNC_Machine/CNC_Machine_CAD_Short/CNC_SHORT_Flexible Coupling 0.25in x 8mm.SLDPRT
20.0 x 20.0 x 25.0 mm
