mjphoto/cnc_machine_mj/CAD_CNC_Machine/CNC_Machine_CAD_Short/CNC_SHORT_Xtreme Solid V Wheel.SLDPRT

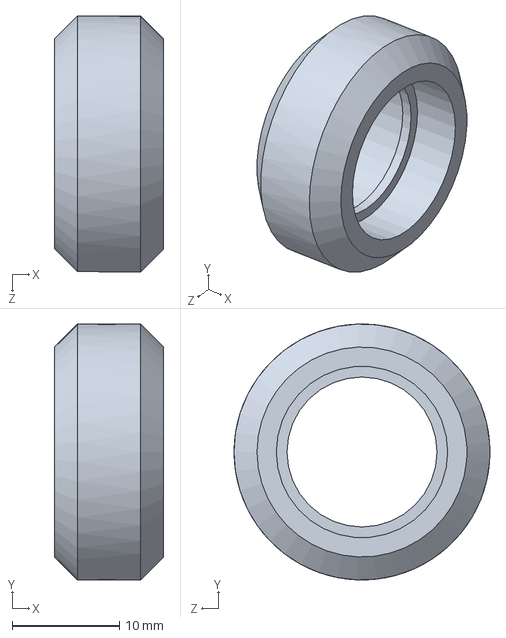
[picture p74: CAD file, 2022-11-07]
CAD_CNC_Machine/CNC_Machine_CAD_Short/CNC_SHORT_Xtreme Solid V Wheel.SLDPRT
10.2 x 23.9 x 23.9 mm
