mjphoto/cnc_machine_mj/CAD_CNC_Machine/CNC_Machine_CAD_Short/CNC_SHORT_Aluminum Spacer 6mm.SLDPRT

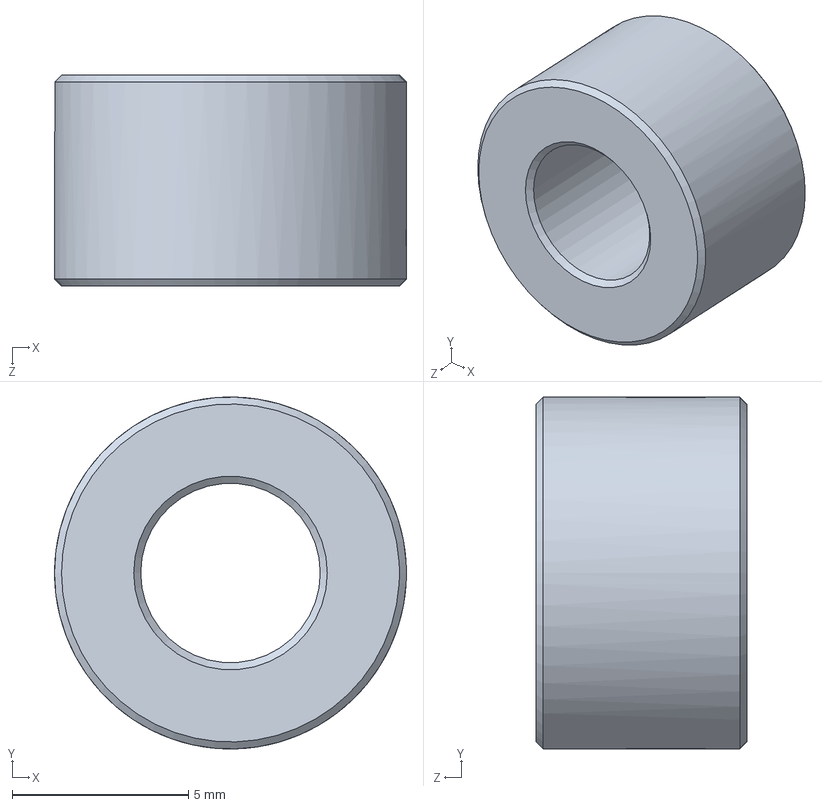
[picture p75: CAD file, 2022-11-07]
CAD_CNC_Machine/CNC_Machine_CAD_Short/CNC_SHORT_Aluminum Spacer 6mm.SLDPRT
10.0 x 10.00 x 6.00 mm
