mjphoto/cnc_machine_mj/CAD_CNC_Machine/CNC_Machine_CAD_Short/CNC_SHORT_Threaded Rod Plate Nema 23.SLDPRT

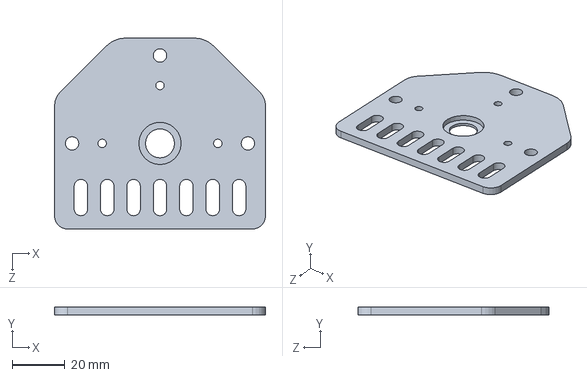
[picture p76: CAD file, 2022-11-07]
CAD_CNC_Machine/CNC_Machine_CAD_Short/CNC_SHORT_Threaded Rod Plate Nema 23.SLDPRT
80.0 x 3.00 x 72.5 mm
