mjphoto/cnc_machine_mj/CAD_CNC_Machine/CNC_Machine_CAD_Short/CNC_SHORT_X Axis Rear Plate_6mm - Build 80_11.15.14.SLDPRT

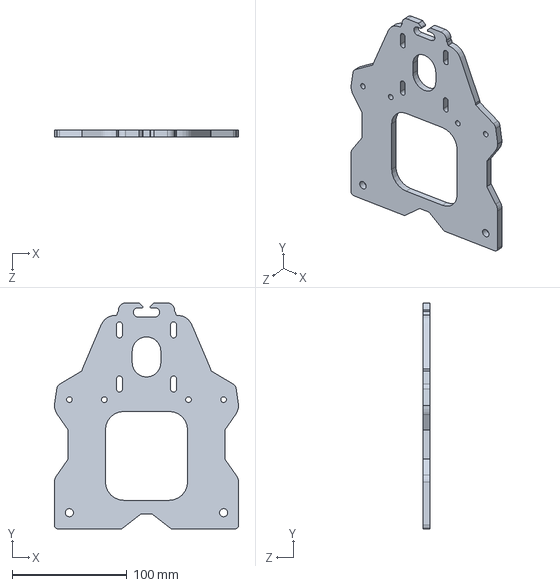
[picture p78: CAD file, 2022-11-07]
CAD_CNC_Machine/CNC_Machine_CAD_Short/CNC_SHORT_X Axis Rear Plate_6mm - Build 80_11.15.14.SLDPRT
160.8 x 197.2 x 6.00 mm
