mjphoto/cnc_machine_mj/CAD_CNC_Machine/CNC_Machine_CAD_Short/CNC_SHORT_Ball Bearing 8 x 16 x 5.SLDPRT

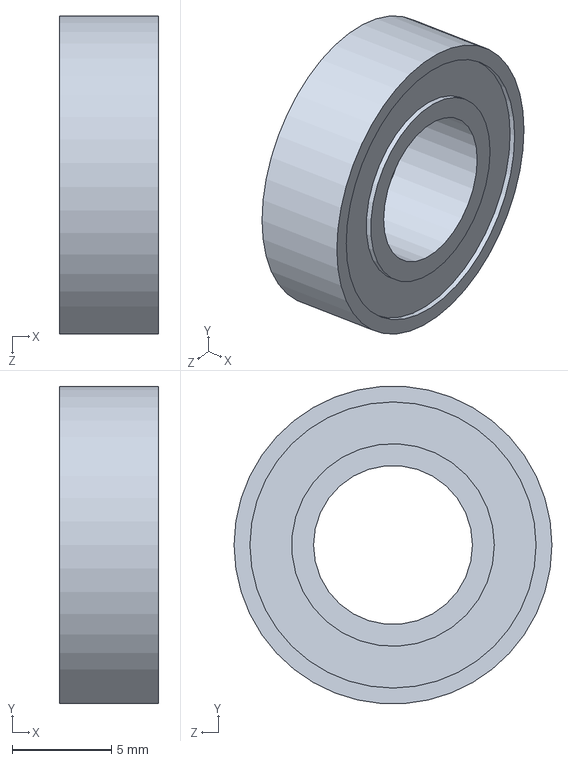
[picture p79: CAD file, 2022-11-07]
CAD_CNC_Machine/CNC_Machine_CAD_Short/CNC_SHORT_Ball Bearing 8 x 16 x 5.SLDPRT
5.00 x 16.0 x 16.0 mm
