mjphoto/cnc_machine_mj/CAD_CNC_Machine/CNC_Machine_CAD_Short/CNC_SHORT_Y Gantry - LArge Plates and Beams.SLDASM

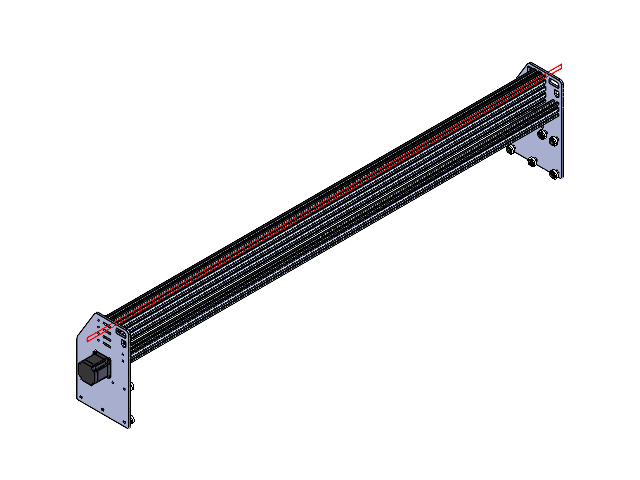
[picture p80: CAD file, 2022-12-09]
CAD_CNC_Machine/CNC_Machine_CAD_Short/CNC_SHORT_Y Gantry - LArge Plates and Beams.SLDASM
CNC_SHORT_Y Gantry Plate_6mm - Build 80_11.15.14 x 2
CNC_SHORT_V-Slot 20x80x1500 Linear Rail x 2
CNC_SHORT_Nema 23 Stepper Motor x 2
CNC_SHORT_GT3 Timing Pulley 20 Tooth x 2
CNC_SHORT_Xtreme Solid V Wheel x 14
CNC_SHORT_Ball Bearing 5 x 16 x 5 x 28
CNC_SHORT_Precision Shim 10 x 5 x 1 x 28
CNC_SHORT_Nylon Insert Lock Nut M5 x 14
CNC_SHORT_Eccentric Spacer 6mm x 6
CNC_SHORT_Aluminum Spacer 6mm x 8
CNC_SHORT_L Bracket Single x 8
CNC_SHORT_V-Slot 20x40x1500 Linear Rail
