mjphoto/cnc_machine_mj/linuxcnc/configs/dev-mill-4microsteps_spindle_control/custom_postgui.hal

# Include your custom_postgui HAL commands here
# This file will not be overwritten when you run stepconf again

# http://7xcnc.com/software/probing/z-touch-plate/
# check this out! http://7xcnc.com/software/linuxcnc/pendant/ joystick
net remote-o100 halui.mdi-command-00 <= pyvcp.o100
net remote-o101 halui.mdi-command-01 <= pyvcp.o101
net remote-o102 halui.mdi-command-02 <= pyvcp.o102
net rapid-to-home halui.mdi-command-03 pyvcp.rapid-to-home

#spindle display
#I commented the follwing 2 lines when debugging spindle comms:
net spindle-at-speed vfd.spindle-at-speed => pyvcp.spindle-at-speed-led
net pyvcp-spindle-rpm   vfd.spindle-speed-fb    => pyvcp.spindle-speed
#net spindle-at-speed => vfd.spindle-at-speed
#last config line read at startup, so enable spindle
#I also commented this one when debugging spindle
setp vfd.enable 1
